Dominik-Workshop/lap-timer/code/Core/Inc/sprites.h

/**
 * @file sprites.h
 * @author Eryk
 * @brief
 * @version 0.1
 * @date 2023-04-27
 *
 * @copyright Copyright (c) 2023
 *
 */

#ifndef SPRITES_H
#define SPRITES_H

#include <stdint.h>

extern const uint8_t *bitmap_deliminator_8_16;
extern const uint8_t *bitmap_lap_timer_logo_128_64;

#endif
